AdamSadkii/Wazza/hardware/wiring/pcb_preview.png

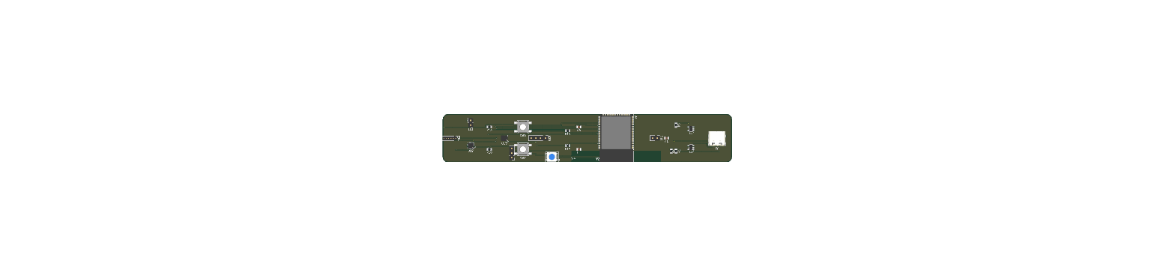
hardware/wiring/pcb_preview.png
