AdamSadkii/Wazza/firmware/src/secrets.example.h

#pragma once

// WiFI Credentials.
#define WIFI_SSID "your-wifi-name"
#define WIFI_PASSWORD "your-wifi-password"

// Backend server configuration.
#define BACKEND_HOST "192.168.1.100"
#define BACKEND_PORT 8765
